kickbxrr/dcs-a10II-arc-210/images/proto-b-2.png

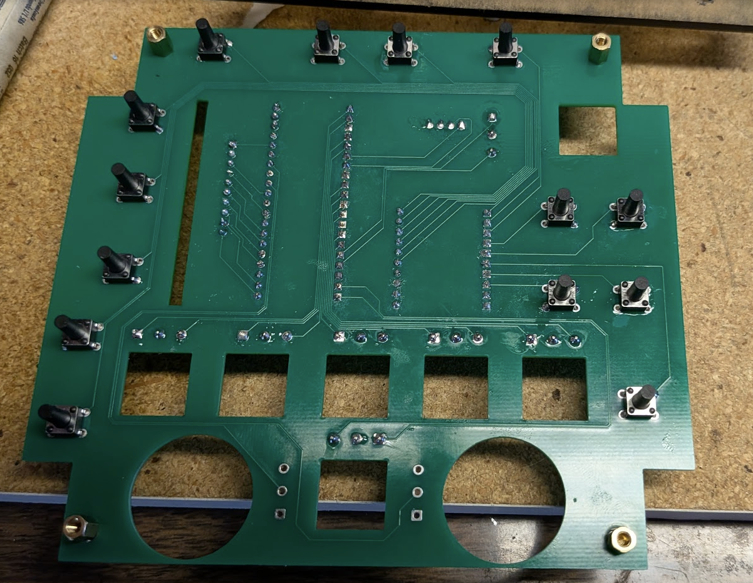
images/proto-b-2.png
