kickbxrr/dcs-a10II-arc-210/arc210_controller/arc210_64_button.h

/*
    16-bit axis gamepad definition
    Copyright (c) 2024 Earle F. Philhower, III <earlephilhower@yahoo.com>

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
    You should have received a copy of the GNU Lesser General Public
    License along with this library; if not, write to the Free Software
    Foundation, Inc., 51 Franklin St, Fifth Floor, Boston, MA  02110-1301  USA
*/

#pragma once

#include "tusb.h"
#include "class/hid/hid_device.h"

#define ARC_210_64_BUTTON(...) \
  HID_USAGE_PAGE ( HID_USAGE_PAGE_DESKTOP     )                 ,\
  HID_USAGE      ( HID_USAGE_DESKTOP_GAMEPAD  )                 ,\
  HID_COLLECTION ( HID_COLLECTION_APPLICATION )                 ,\
    /* Report ID if any */\
    __VA_ARGS__ \
     /* 16 bit X, Y, Z, Rz, Rx, Ry (min -32767, max 32767 ) */ \
    HID_USAGE_PAGE     ( HID_USAGE_PAGE_DESKTOP                 ) ,\
    HID_USAGE          ( HID_USAGE_DESKTOP_X                    ) ,\
    HID_USAGE          ( HID_USAGE_DESKTOP_Y                    ) ,\
    HID_USAGE          ( HID_USAGE_DESKTOP_Z                    ) ,\
    HID_USAGE          ( HID_USAGE_DESKTOP_RZ                   ) ,\
    HID_USAGE          ( HID_USAGE_DESKTOP_RX                   ) ,\
    HID_USAGE          ( HID_USAGE_DESKTOP_RY                   ) ,\
    HID_LOGICAL_MIN_N  ( -32767, 2                              ) ,\
    HID_LOGICAL_MAX_N  ( 32767, 2                               ) ,\
    HID_REPORT_COUNT   ( 6                                      ) ,\
    HID_REPORT_SIZE    ( 16                                     ) ,\
    HID_INPUT          ( HID_DATA | HID_VARIABLE | HID_ABSOLUTE ) ,\
    /* 8 bit DPad/Hat Button Map  */ \
    HID_USAGE_PAGE     ( HID_USAGE_PAGE_DESKTOP                 ) ,\
    HID_USAGE          ( HID_USAGE_DESKTOP_HAT_SWITCH           ) ,\
    HID_LOGICAL_MIN    ( 1                                      ) ,\
    HID_LOGICAL_MAX    ( 8                                      ) ,\
    HID_PHYSICAL_MIN   ( 0                                      ) ,\
    HID_PHYSICAL_MAX_N ( 315, 2                                 ) ,\
    HID_REPORT_COUNT   ( 1                                      ) ,\
    HID_REPORT_SIZE    ( 8                                      ) ,\
    HID_INPUT          ( HID_DATA | HID_VARIABLE | HID_ABSOLUTE ) ,\
    /* 32 bit Button Map */ \
    HID_USAGE_PAGE     ( HID_USAGE_PAGE_BUTTON                  ) ,\
    HID_USAGE_MIN      ( 1                                      ) ,\
    HID_USAGE_MAX      ( 32                                     ) ,\
    HID_LOGICAL_MIN    ( 0                                      ) ,\
    HID_LOGICAL_MAX    ( 1                                      ) ,\
    HID_REPORT_COUNT   ( 32                                     ) ,\
    HID_REPORT_SIZE    ( 1                                      ) ,\
    HID_INPUT          ( HID_DATA | HID_VARIABLE | HID_ABSOLUTE ) ,\
    /* 32 bit Button Map */ \
    HID_USAGE_PAGE     ( HID_USAGE_PAGE_BUTTON                  ) ,\
    HID_USAGE_MIN      ( 1                                      ) ,\
    HID_USAGE_MAX      ( 32                                     ) ,\
    HID_LOGICAL_MIN    ( 0                                      ) ,\
    HID_LOGICAL_MAX    ( 1                                      ) ,\
    HID_REPORT_COUNT   ( 32                                     ) ,\
    HID_REPORT_SIZE    ( 1                                      ) ,\
    HID_INPUT          ( HID_DATA | HID_VARIABLE | HID_ABSOLUTE ) ,\
  HID_COLLECTION_END \

#include "arc210_64_button_report.h"
